TAUFEEQ1/floodwall-/simulations/5/barrier_foundation.stp

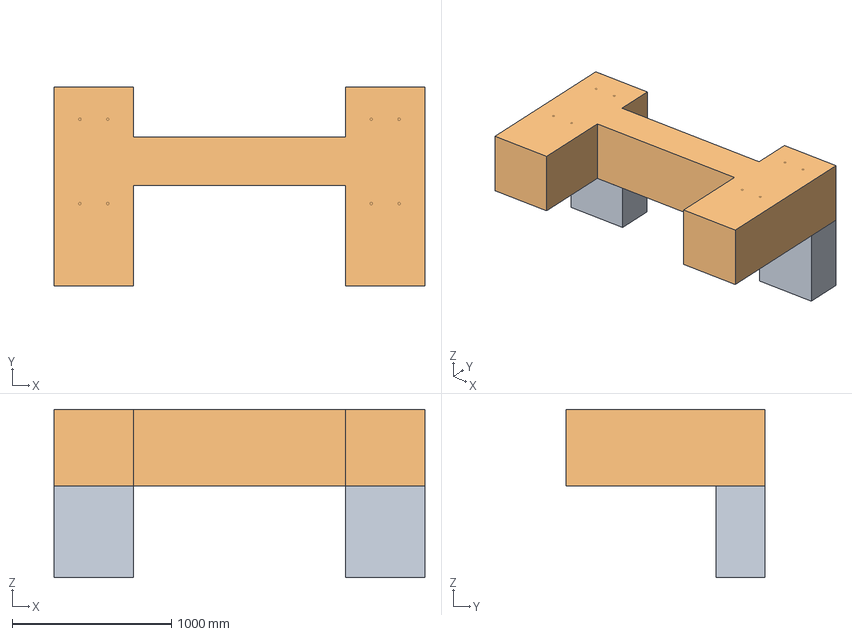
[picture p69: CAD file, 2018-06-25, an earlier design]
simulations/5/barrier_foundation.stp
2326.4 x 1248.4 x 1055.1 mm
