TAUFEEQ1/floodwall-/simulations/5/wall_span.stp

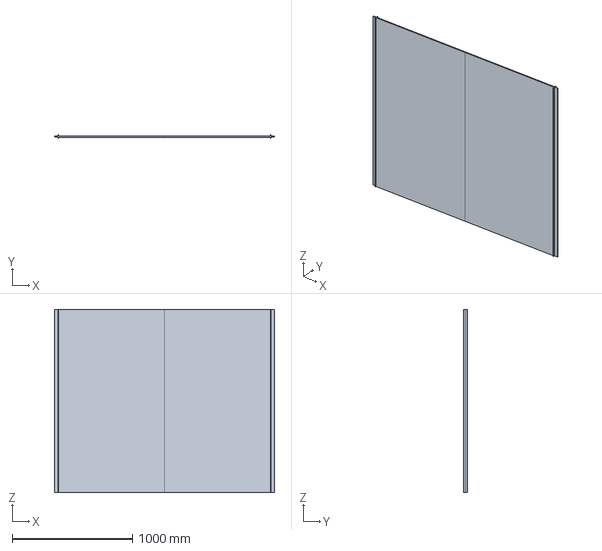
[picture p70: CAD file, 2018-06-25, an earlier design]
simulations/5/wall_span.stp
1827.0 x 31.6 x 1522.5 mm
