TAUFEEQ1/floodwall-/simulations/5/flange.stp

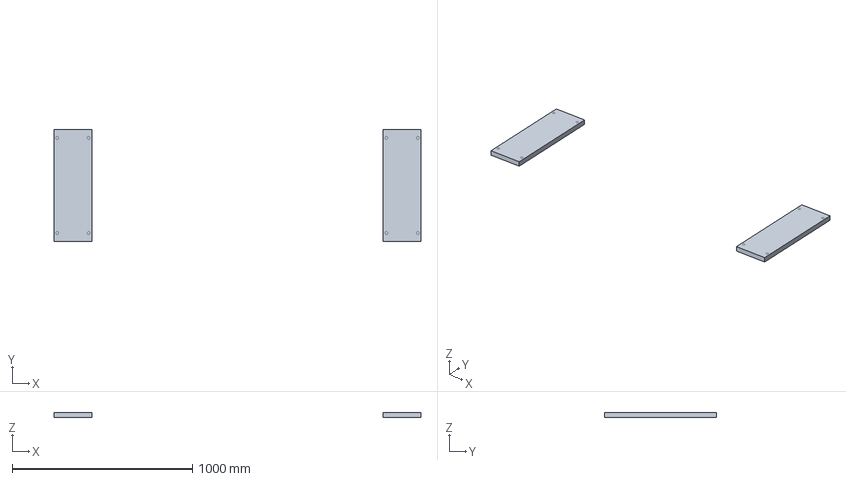
[picture p71: CAD file, 2018-06-25, an earlier design]
simulations/5/flange.stp
2037.0 x 622.6 x 30.0 mm
