TAUFEEQ1/floodwall-/simulations/5/barrier_base.stp

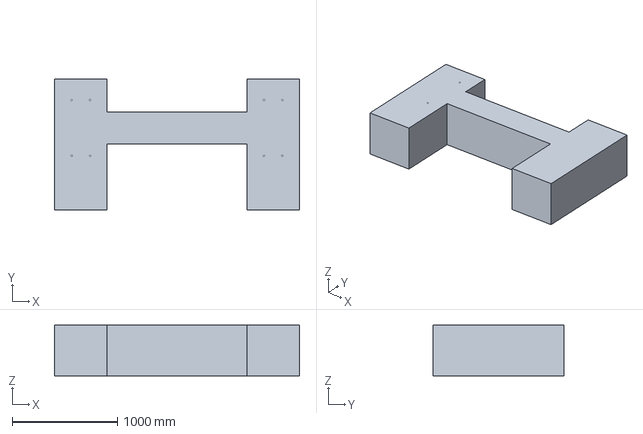
[picture p72: CAD file, 2018-06-25, an earlier design]
simulations/5/barrier_base.stp
2326.4 x 1248.4 x 479.6 mm
